joshhead/fsr-dance-pad/images/061-bar-mounting-hardware-2-wide.jpg

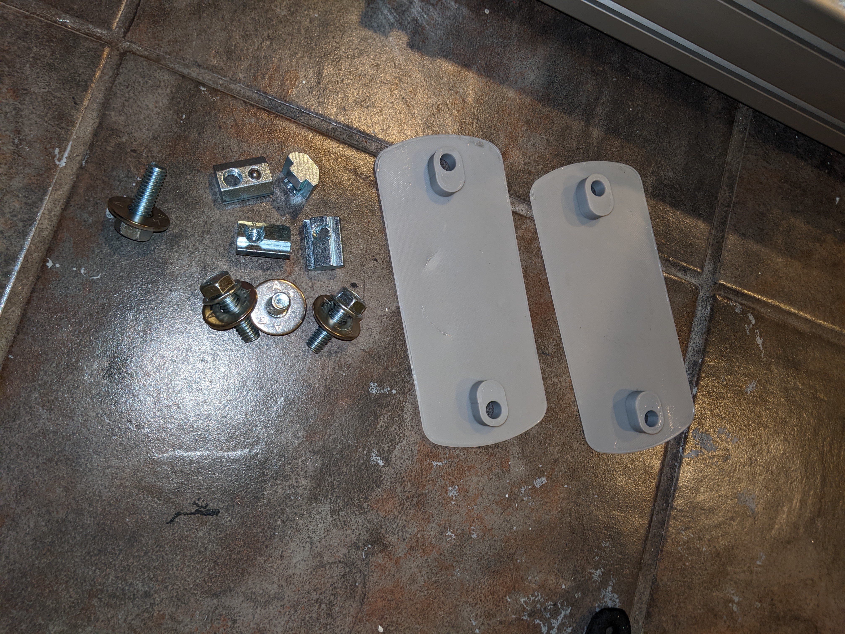
images/061-bar-mounting-hardware-2-wide.jpg
