joshhead/fsr-dance-pad/images/arrow.png

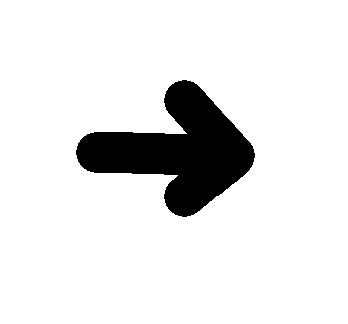
images/arrow.png
