joshhead/fsr-dance-pad/freecad/parts-and-subassemblies/breadboard-holder.FCStd

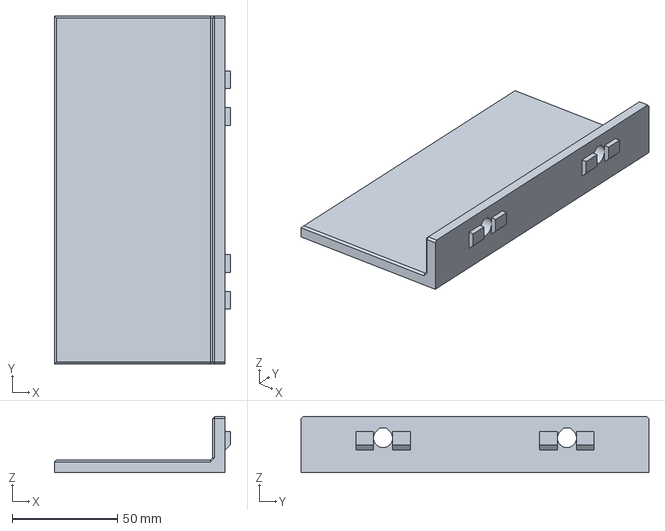
[picture p86: CAD file, 2024-04-13]
freecad/parts-and-subassemblies/breadboard-holder.FCStd
83.6 x 165.0 x 26.6 mm
