joshhead/fsr-dance-pad/step/inactive-panel-standoff.step

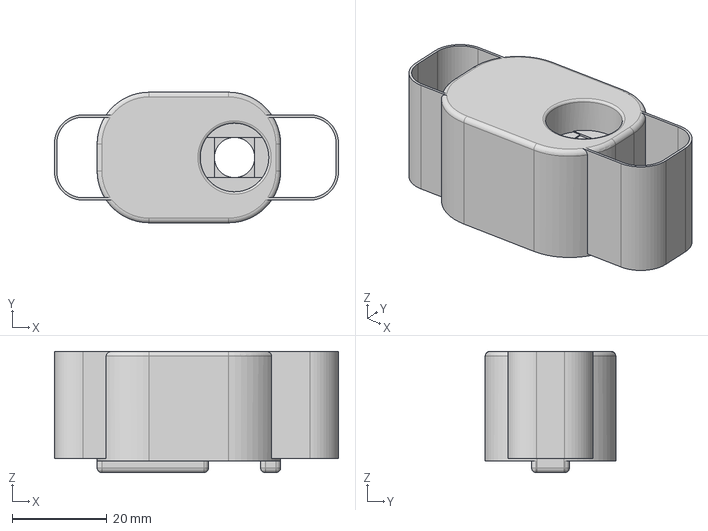
[picture p87: CAD file, 2023-12-29]
step/inactive-panel-standoff.step
60.0 x 27.6 x 25.6 mm
