joshhead/fsr-dance-pad/stl/fsr-holder.stl

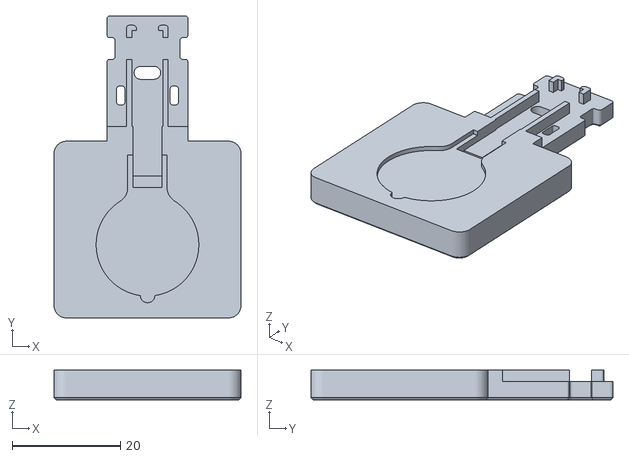
[picture p88: CAD file, 2023-01-10]
stl/fsr-holder.stl
34.6 x 55.8 x 5.50
