joshhead/fsr-dance-pad/freecad/parts-and-subassemblies/plastic-end-cap-retainer.FCStd

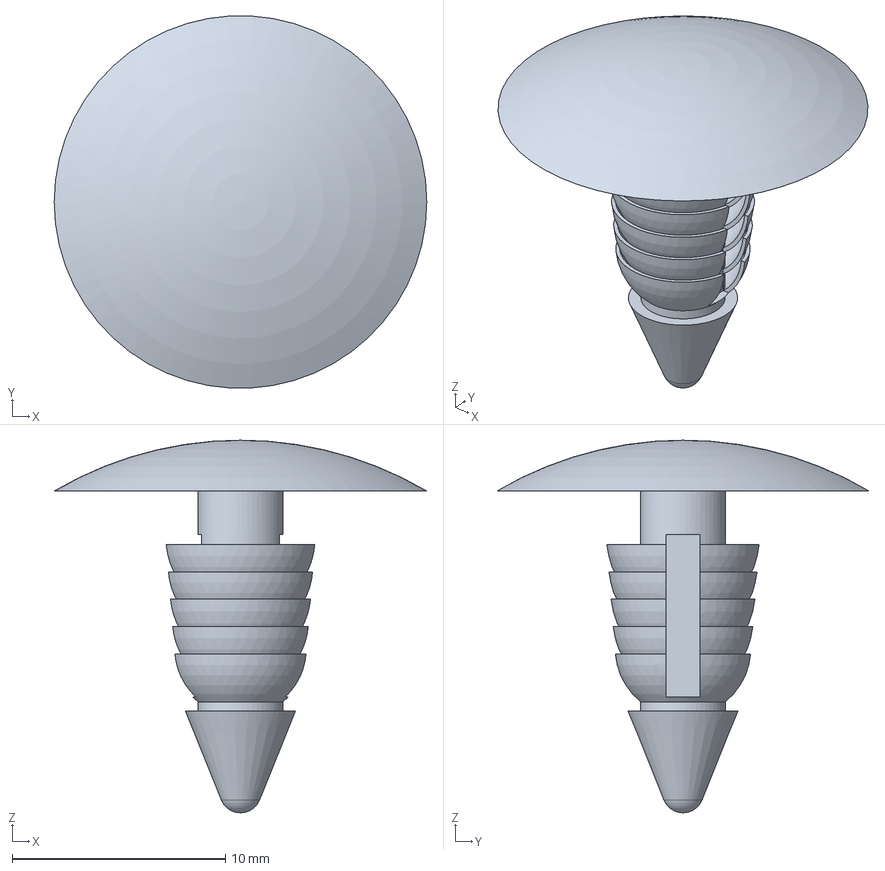
[picture p89: CAD file, 2024-04-13]
freecad/parts-and-subassemblies/plastic-end-cap-retainer.FCStd
17.5 x 17.4 x 17.5 mm
