joshhead/fsr-dance-pad/stl/tool-sensor-spacer.stl

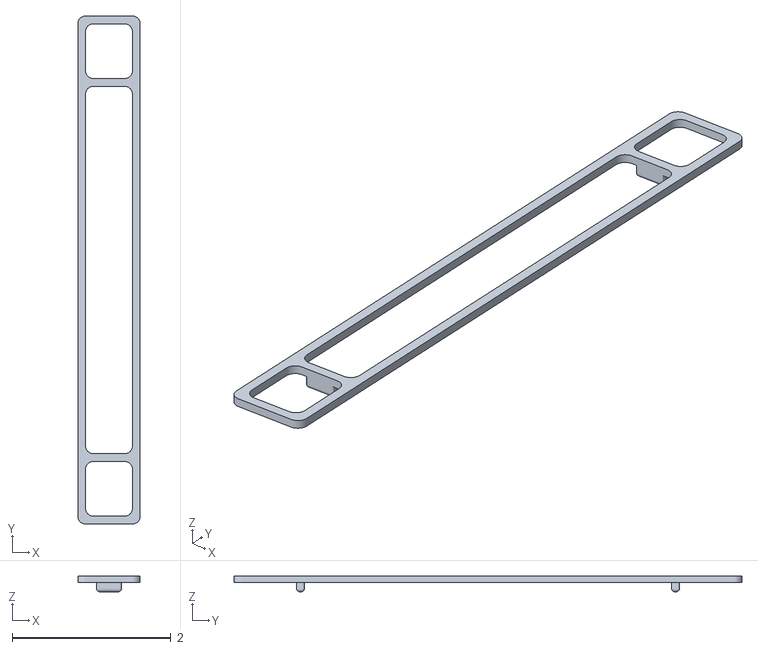
[picture p90: CAD file, 2023-01-10]
stl/tool-sensor-spacer.stl
0.787 x 6.40 x 0.197
