joshhead/fsr-dance-pad/stl/tool-hook-and-loop-dot-aligner.stl

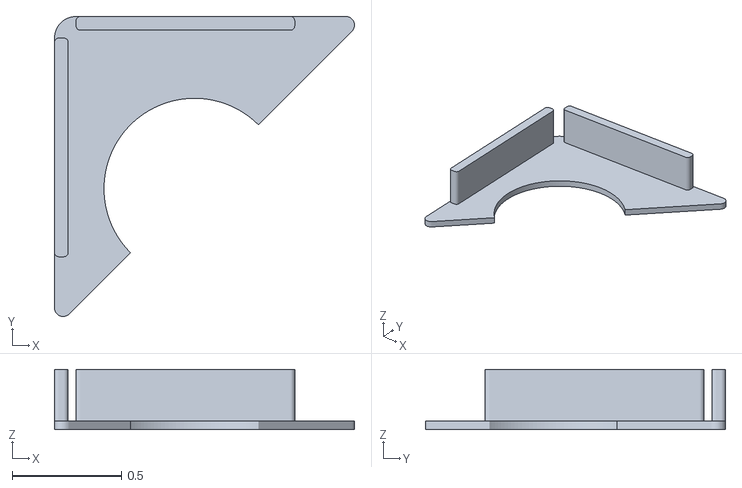
[picture p91: CAD file, 2023-01-10]
stl/tool-hook-and-loop-dot-aligner.stl
1.37 x 1.37 x 0.276
