joshhead/fsr-dance-pad/freecad/parts-and-subassemblies/anchor-fastener-cam.FCStd

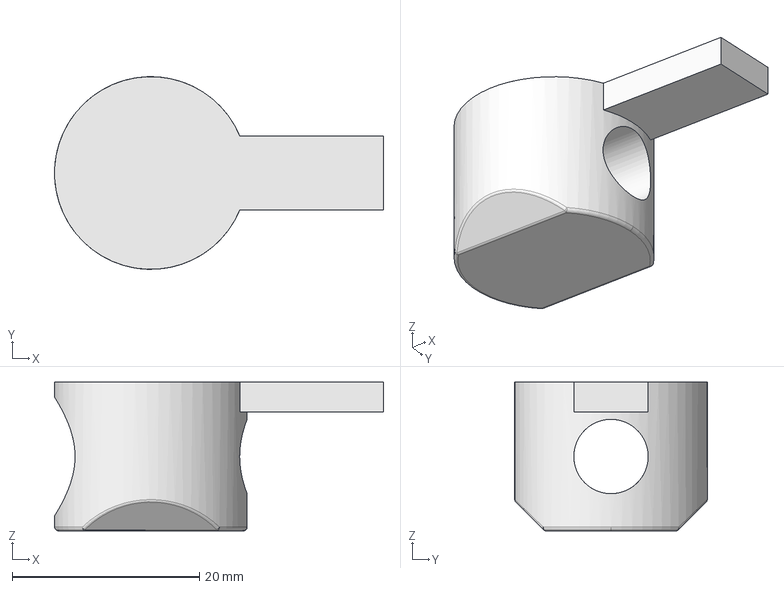
[picture p92: CAD file, 2024-04-13]
freecad/parts-and-subassemblies/anchor-fastener-cam.FCStd
35.1 x 20.6 x 15.9 mm
