joshhead/fsr-dance-pad/stl/fsr-standoff.stl

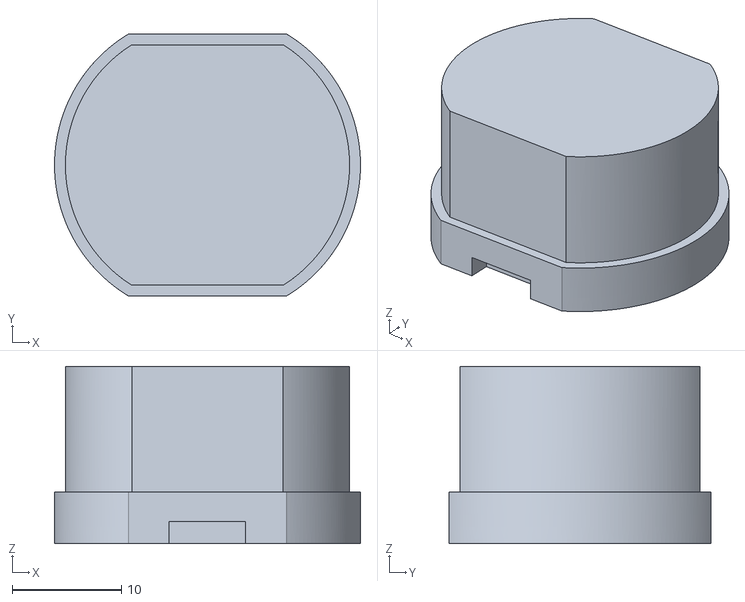
[picture p93: CAD file, 2023-01-10]
stl/fsr-standoff.stl
28.0 x 24.0 x 16.2
