joshhead/fsr-dance-pad/freecad/parts-and-subassemblies/active-panel-standoff.FCStd

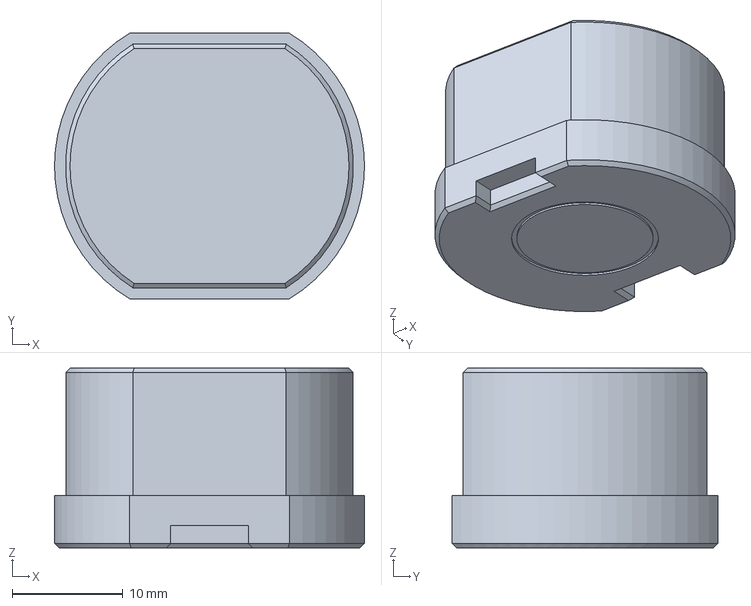
[picture p94: CAD file, 2024-04-13]
freecad/parts-and-subassemblies/active-panel-standoff.FCStd
28.0 x 24.0 x 16.2 mm
