joshhead/fsr-dance-pad/freecad/parts-and-subassemblies/solderless-breadboard.FCStd

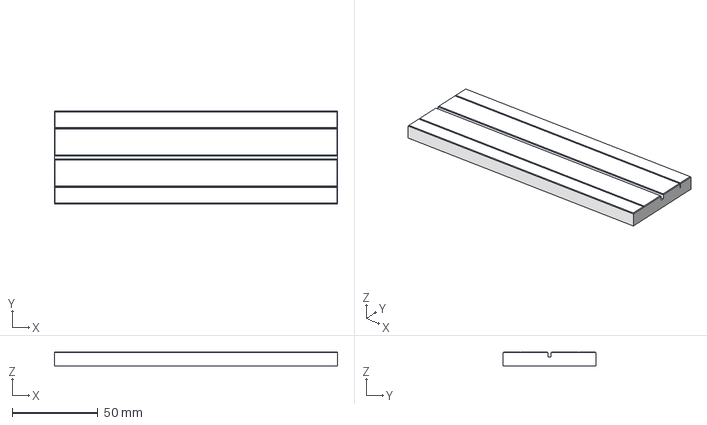
[picture p95: CAD file, 2024-04-13]
freecad/parts-and-subassemblies/solderless-breadboard.FCStd
165.0 x 54.0 x 8.40 mm
