joshhead/fsr-dance-pad/freecad/parts-and-subassemblies/safety-rail-flange.FCStd

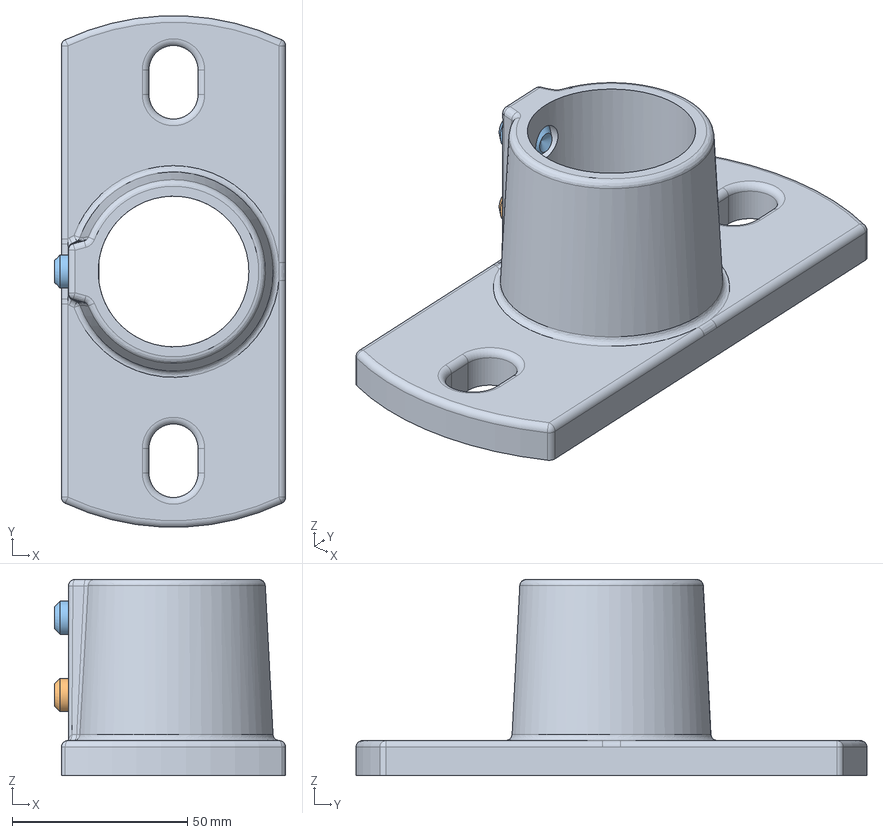
[picture p96: CAD file, 2024-04-13]
freecad/parts-and-subassemblies/safety-rail-flange.FCStd
66.0 x 145.8 x 56.0 mm
3/8inx1/2in-Screw
3/8inx1/2in-Screw001
