joshhead/fsr-dance-pad/freecad/parts-and-subassemblies/microcontroller-board.FCStd

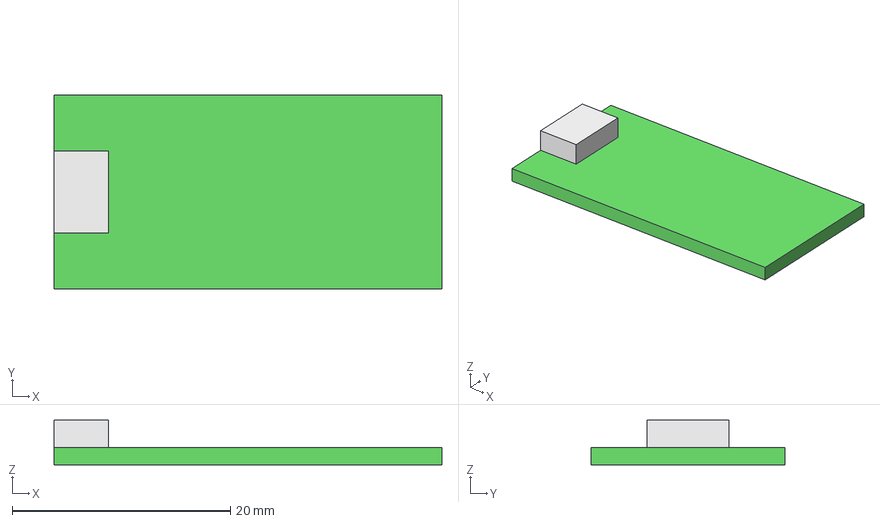
[picture p98: CAD file, 2024-04-13]
freecad/parts-and-subassemblies/microcontroller-board.FCStd
35.6 x 17.8 x 4.10 mm
PCB
USB Receptacle
