joshhead/fsr-dance-pad/freecad/parts-and-subassemblies/inactive-panel-standoff.FCStd

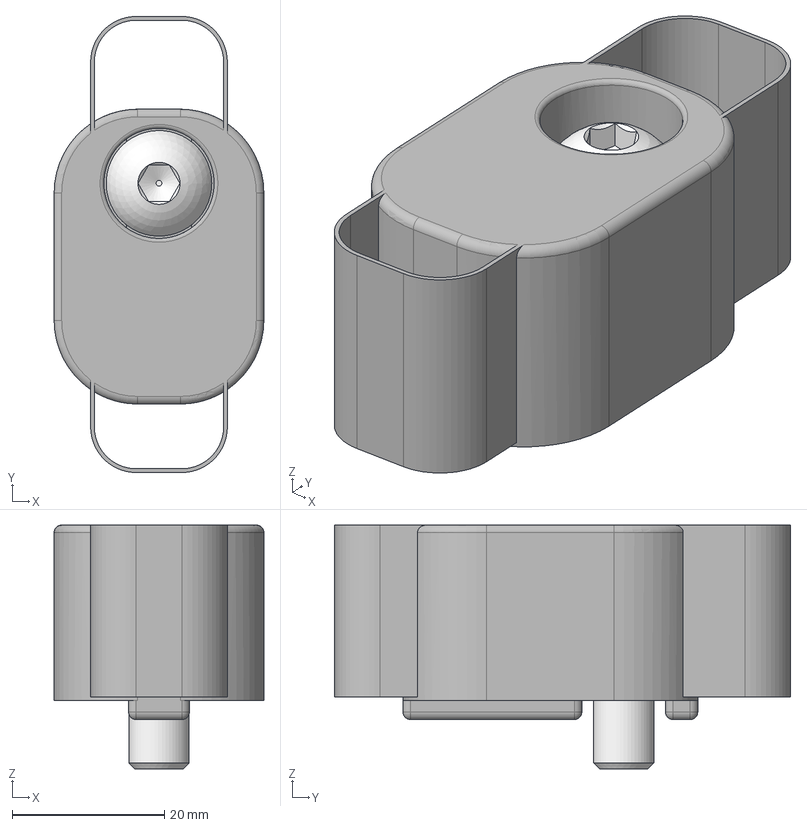
[picture p99: CAD file, 2024-04-13]
freecad/parts-and-subassemblies/inactive-panel-standoff.FCStd
27.6 x 60.0 x 32.1 mm
5/16inx1in-Screw
