joshhead/fsr-dance-pad/freecad/parts-and-subassemblies/1530UL-33.375-FGIFGI-counterbore.FCStd

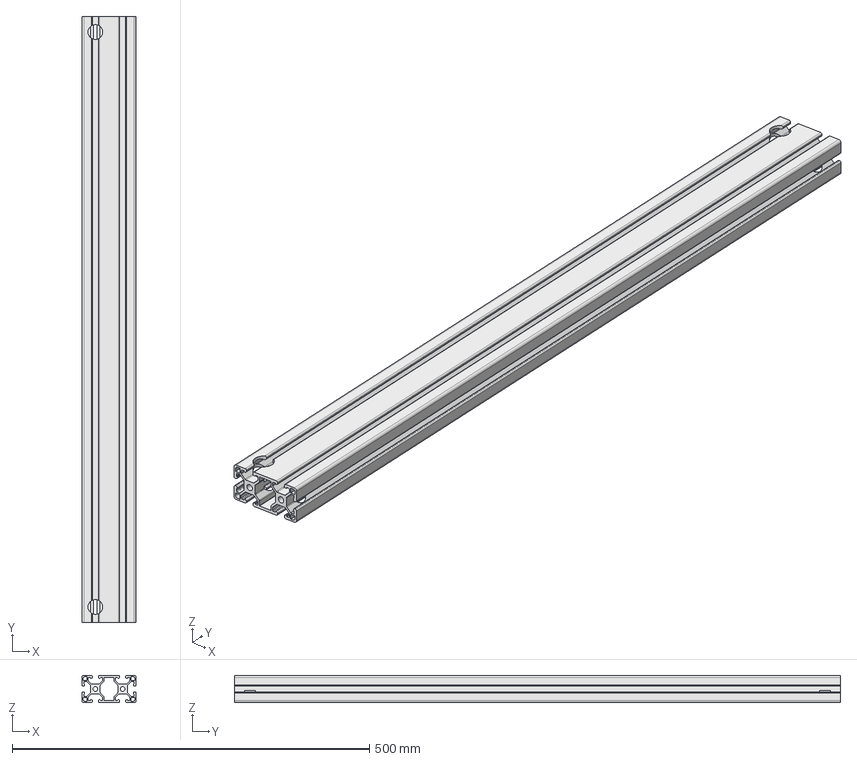
[picture p100: CAD file, 2024-04-13]
freecad/parts-and-subassemblies/1530UL-33.375-FGIFGI-counterbore.FCStd
76.2 x 847.7 x 38.1 mm
