joshhead/fsr-dance-pad/freecad/parts-and-subassemblies/hook-and-loop-dot-pair.FCStd

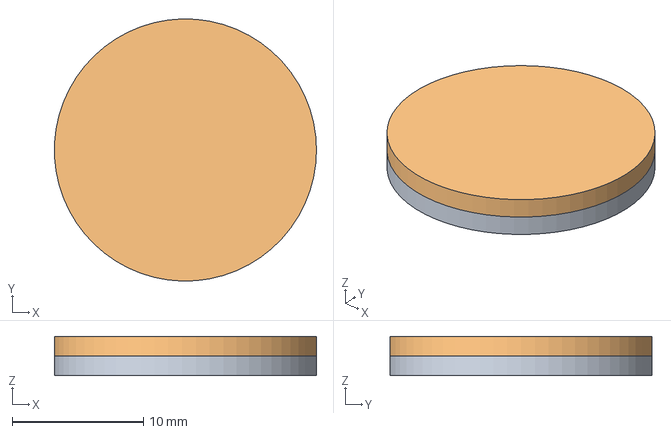
[picture p101: CAD file, 2024-04-13]
freecad/parts-and-subassemblies/hook-and-loop-dot-pair.FCStd
20.0 x 20.0 x 3.00 mm
