joshhead/fsr-dance-pad/freecad/parts-and-subassemblies/pump-it-up-gx-bar.FCStd

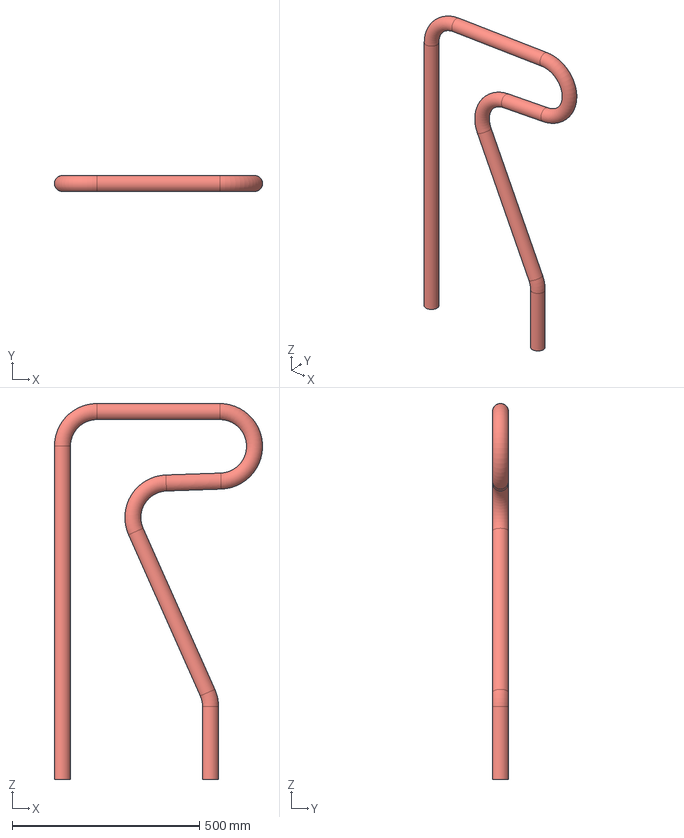
[picture p102: CAD file, 2024-04-13]
freecad/parts-and-subassemblies/pump-it-up-gx-bar.FCStd
555.4 x 43.0 x 1003.3 mm
