joshhead/fsr-dance-pad/freecad/parts-and-subassemblies/1515-33.375-ACAC-counterbore.FCStd

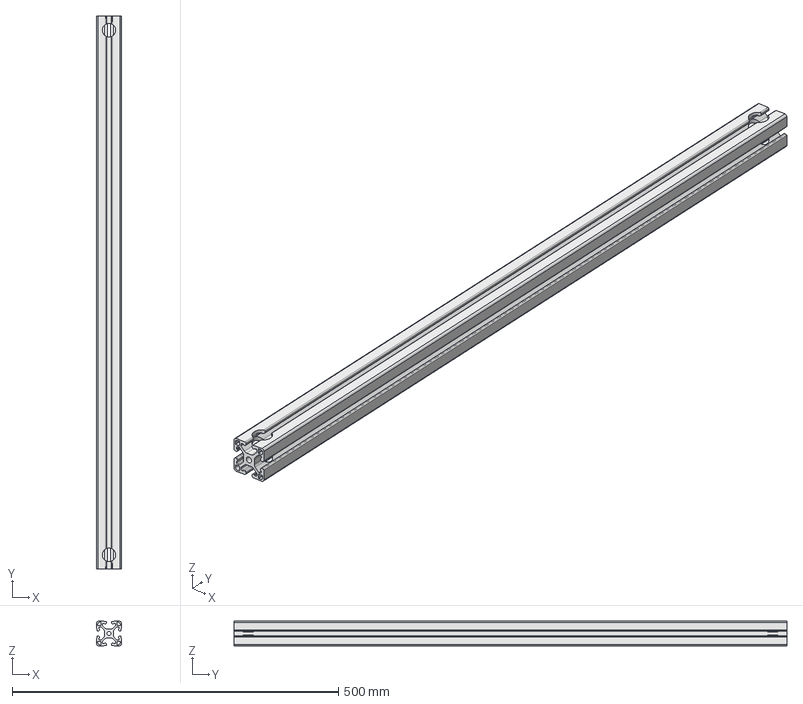
[picture p103: CAD file, 2024-04-13]
freecad/parts-and-subassemblies/1515-33.375-ACAC-counterbore.FCStd
38.0 x 847.7 x 38.0 mm
