joshhead/fsr-dance-pad/freecad/parts-and-subassemblies/rubber-bumper.FCStd

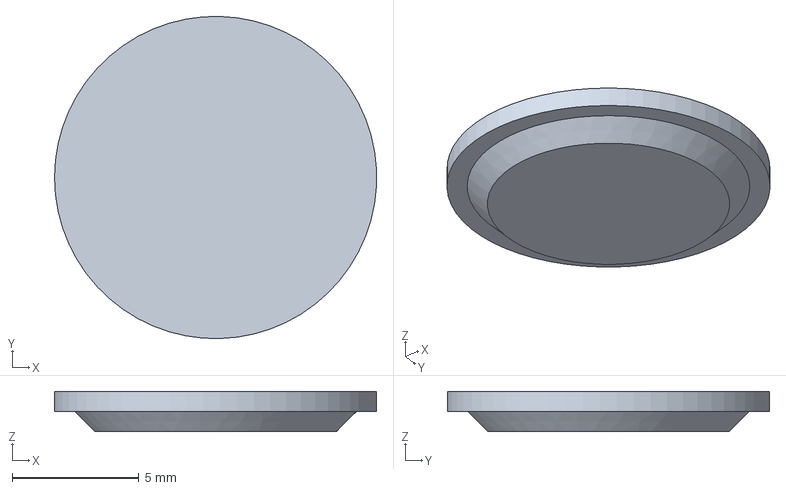
[picture p104: CAD file, 2024-04-13]
freecad/parts-and-subassemblies/rubber-bumper.FCStd
12.7 x 12.7 x 1.59 mm
