joshhead/fsr-dance-pad/freecad/parts-and-subassemblies/interlink-female-connector-housing.FCStd

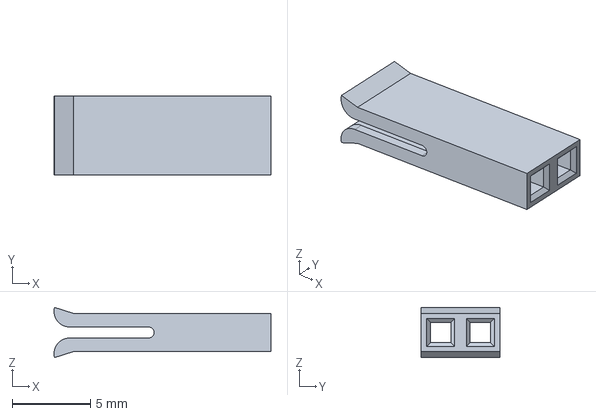
[picture p105: CAD file, 2024-04-13]
freecad/parts-and-subassemblies/interlink-female-connector-housing.FCStd
13.8 x 5.05 x 3.20 mm
