joshhead/fsr-dance-pad/freecad/parts-and-subassemblies/fsr-402-short.FCStd

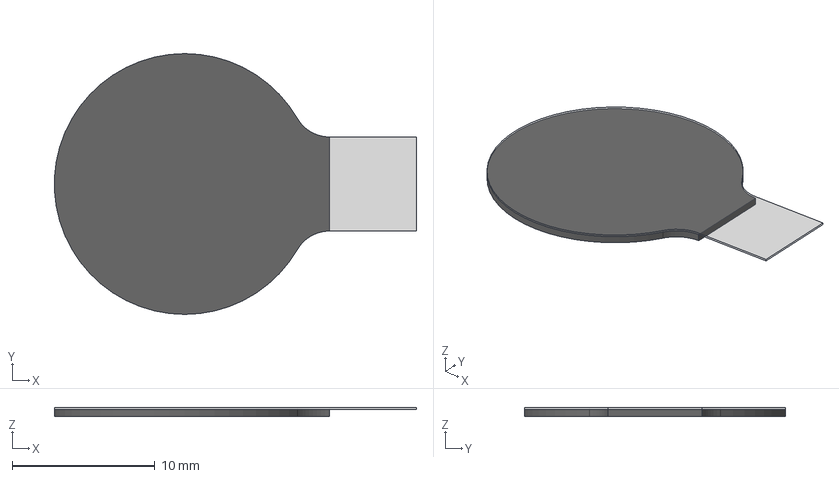
[picture p106: CAD file, 2024-04-13]
freecad/parts-and-subassemblies/fsr-402-short.FCStd
25.4 x 18.3 x 0.63 mm
Film
Stackup
