joshhead/fsr-dance-pad/freecad/parts-and-subassemblies/plastic-end-cap-1530.FCStd

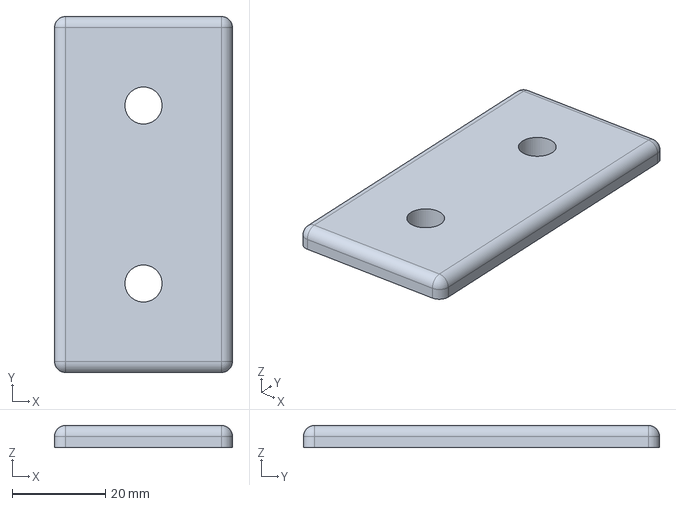
[picture p107: CAD file, 2024-04-13]
freecad/parts-and-subassemblies/plastic-end-cap-1530.FCStd
38.1 x 76.2 x 4.76 mm
