joshhead/fsr-dance-pad/freecad/parts-and-subassemblies/acrylic-panel.FCStd

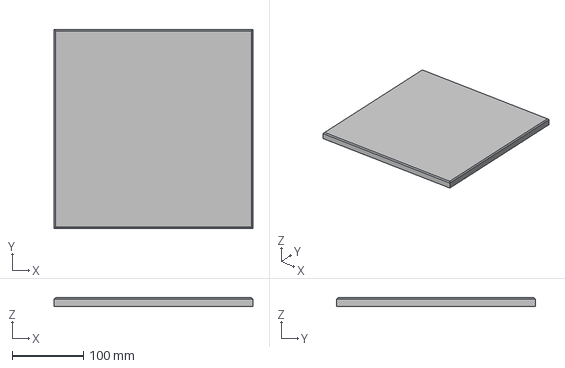
[picture p108: CAD file, 2024-04-13]
freecad/parts-and-subassemblies/acrylic-panel.FCStd
279.4 x 279.4 x 12.0 mm
