joshhead/fsr-dance-pad/freecad/parts-and-subassemblies/1530UL-40.875.FCStd

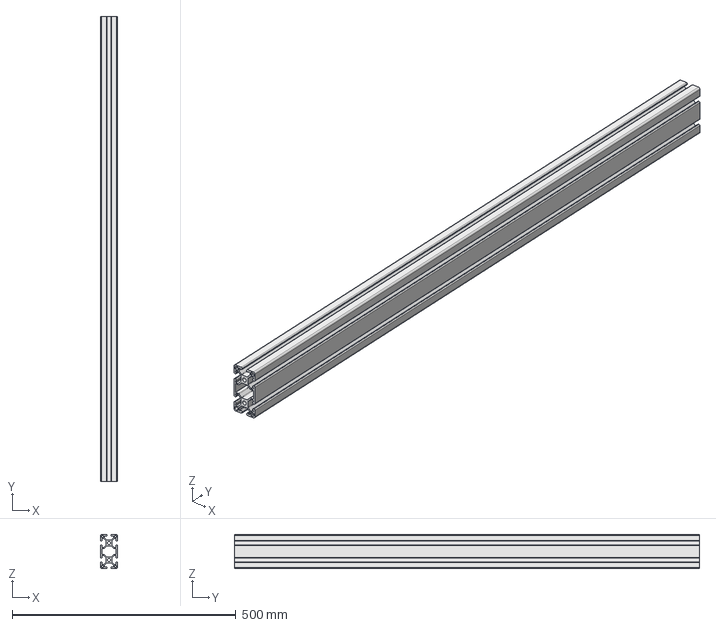
[picture p109: CAD file, 2024-04-13]
freecad/parts-and-subassemblies/1530UL-40.875.FCStd
38.1 x 1038.2 x 76.2 mm
