joshhead/fsr-dance-pad/freecad/parts-and-subassemblies/3060-33.375-KLO-counterbore.FCStd

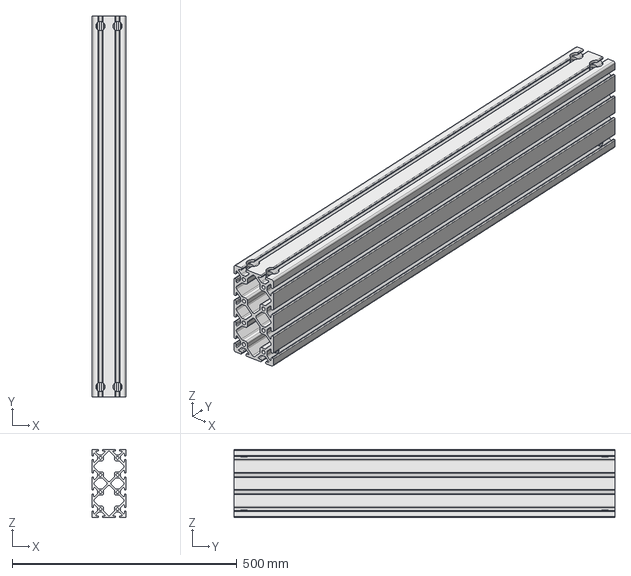
[picture p110: CAD file, 2024-04-13]
freecad/parts-and-subassemblies/3060-33.375-KLO-counterbore.FCStd
76.2 x 847.7 x 152.4 mm
